luftaquila/monolith/device/TMA-1/Core/Src/sdio.c

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
/* Includes ------------------------------------------------------------------*/
#include "sdio.h"

/* USER CODE BEGIN 0 */
extern FIL logfile;
extern SYSTEM_STATE sys_state;
char logname[40];

LOG syslog_buffer;
extern ring_buffer_t SD_BUFFER;
extern uint8_t SD_BUFFER_ARR[1 << 12];

int SD_SETUP(DATETIME *boot) {
  FATFS SD_FATFS;

  // init buffer
  ring_buffer_init(&SD_BUFFER, (char *)SD_BUFFER_ARR, sizeof(SD_BUFFER_ARR));

  disk_initialize((BYTE) 0);
  int ret = f_mount(&SD_FATFS, "", 0);

  if (ret != FR_OK) {
    sys_state.SD = false;
    HAL_GPIO_WritePin(GPIOE, LED_SD_Pin, GPIO_PIN_RESET);

    DEBUG_MSG("[%8lu] [ERR] SD mount failed: %d\r\n", HAL_GetTick(), ret);
    SYS_LOG(LOG_ERROR, SYS, SYS_SD_FAIL);

    return ret;
  }

  sprintf(logname, "20%02d-%02d-%02d %02d-%02d-%02d.log",
      boot->year, boot->month, boot->date, boot->hour, boot->minute, boot->second);

  ret = f_open(&logfile, logname, FA_OPEN_APPEND | FA_WRITE);

  if (ret != FR_OK) {
    sys_state.SD = false;
    HAL_GPIO_WritePin(GPIOE, LED_SD_Pin, GPIO_PIN_RESET);

    DEBUG_MSG("[%8lu] [ERR] SD open failed: %d\r\n", HAL_GetTick(), ret);
    SYS_LOG(LOG_ERROR, SYS, SYS_SD_FAIL);

    return ret;
  }

  sys_state.SD = true;
  HAL_GPIO_WritePin(GPIOE, LED_SD_Pin, GPIO_PIN_SET);

  return SYS_OK;
}

int SD_WRITE(void) {
  if (sys_state.SD == false) {
    return -1;
  }

  if (ring_buffer_is_empty(&SD_BUFFER)) {
    return -1;
  }

  int ret = 0;
  static int32_t written_count;

  while (!ring_buffer_is_empty(&SD_BUFFER)) {
    ring_buffer_dequeue_arr(&SD_BUFFER, (char *)&syslog_buffer, sizeof(LOG));
    ret = f_write(&logfile, &syslog_buffer, sizeof(LOG), (void *)&written_count);
  }

  if (ret != FR_OK) {
    sys_state.SD = false;
    HAL_GPIO_WritePin(GPIOE, LED_SD_Pin, GPIO_PIN_RESET);

    DEBUG_MSG("[%8lu] [ERR] SD write failed: %d\r\n", HAL_GetTick(), ret);
    SYS_LOG(LOG_ERROR, SYS, SYS_SD_FAIL);
  }

  return ret;
}

int SD_SYNC(void) {
  if (sys_state.SD == false) {
    return -1;
  }

  int ret = f_sync(&logfile);

  if (ret != FR_OK) {
    sys_state.SD = false;
    HAL_GPIO_WritePin(GPIOE, LED_SD_Pin, GPIO_PIN_RESET);

    DEBUG_MSG("[%8lu] [ERR] SD sync failed: %d\r\n", HAL_GetTick(), ret);
    SYS_LOG(LOG_ERROR, SYS, SYS_SD_FAIL);
  }

  return ret;
}
/* USER CODE END 0 */

SD_HandleTypeDef hsd;
DMA_HandleTypeDef hdma_sdio_rx;
DMA_HandleTypeDef hdma_sdio_tx;

/* SDIO init function */

void MX_SDIO_SD_Init(void)
{

  hsd.Instance = SDIO;
  hsd.Init.ClockEdge = SDIO_CLOCK_EDGE_RISING;
  hsd.Init.ClockBypass = SDIO_CLOCK_BYPASS_DISABLE;
  hsd.Init.ClockPowerSave = SDIO_CLOCK_POWER_SAVE_DISABLE;
  hsd.Init.BusWide = SDIO_BUS_WIDE_1B;
  hsd.Init.HardwareFlowControl = SDIO_HARDWARE_FLOW_CONTROL_ENABLE;
  hsd.Init.ClockDiv = 12;
}

void HAL_SD_MspInit(SD_HandleTypeDef* sdHandle)
{

  GPIO_InitTypeDef GPIO_InitStruct = {0};
  if(sdHandle->Instance==SDIO)
  {
    /* SDIO clock enable */
    __HAL_RCC_SDIO_CLK_ENABLE();

    __HAL_RCC_GPIOC_CLK_ENABLE();
    __HAL_RCC_GPIOD_CLK_ENABLE();
    /**SDIO GPIO Configuration
    PC8     ------> SDIO_D0
    PC12     ------> SDIO_CK
    PD2     ------> SDIO_CMD
    */
    GPIO_InitStruct.Pin = GPIO_PIN_8;
    GPIO_InitStruct.Mode = GPIO_MODE_AF_PP;
    GPIO_InitStruct.Pull = GPIO_PULLUP;
    GPIO_InitStruct.Speed = GPIO_SPEED_FREQ_VERY_HIGH;
    GPIO_InitStruct.Alternate = GPIO_AF12_SDIO;
    HAL_GPIO_Init(GPIOC, &GPIO_InitStruct);

    GPIO_InitStruct.Pin = GPIO_PIN_12;
    GPIO_InitStruct.Mode = GPIO_MODE_AF_PP;
    GPIO_InitStruct.Pull = GPIO_NOPULL;
    GPIO_InitStruct.Speed = GPIO_SPEED_FREQ_VERY_HIGH;
    GPIO_InitStruct.Alternate = GPIO_AF12_SDIO;
    HAL_GPIO_Init(GPIOC, &GPIO_InitStruct);

    GPIO_InitStruct.Pin = GPIO_PIN_2;
    GPIO_InitStruct.Mode = GPIO_MODE_AF_PP;
    GPIO_InitStruct.Pull = GPIO_PULLUP;
    GPIO_InitStruct.Speed = GPIO_SPEED_FREQ_VERY_HIGH;
    GPIO_InitStruct.Alternate = GPIO_AF12_SDIO;
    HAL_GPIO_Init(GPIOD, &GPIO_InitStruct);

    /* SDIO DMA Init */
    /* SDIO_RX Init */
    hdma_sdio_rx.Instance = DMA2_Stream6;
    hdma_sdio_rx.Init.Channel = DMA_CHANNEL_4;
    hdma_sdio_rx.Init.Direction = DMA_PERIPH_TO_MEMORY;
    hdma_sdio_rx.Init.PeriphInc = DMA_PINC_DISABLE;
    hdma_sdio_rx.Init.MemInc = DMA_MINC_ENABLE;
    hdma_sdio_rx.Init.PeriphDataAlignment = DMA_PDATAALIGN_WORD;
    hdma_sdio_rx.Init.MemDataAlignment = DMA_MDATAALIGN_WORD;
    hdma_sdio_rx.Init.Mode = DMA_PFCTRL;
    hdma_sdio_rx.Init.Priority = DMA_PRIORITY_LOW;
    hdma_sdio_rx.Init.FIFOMode = DMA_FIFOMODE_ENABLE;
    hdma_sdio_rx.Init.FIFOThreshold = DMA_FIFO_THRESHOLD_FULL;
    hdma_sdio_rx.Init.MemBurst = DMA_MBURST_INC4;
    hdma_sdio_rx.Init.PeriphBurst = DMA_PBURST_INC4;
    if (HAL_DMA_Init(&hdma_sdio_rx) != HAL_OK)
    {
      Error_Handler();
    }

    __HAL_LINKDMA(sdHandle,hdmarx,hdma_sdio_rx);

    /* SDIO_TX Init */
    hdma_sdio_tx.Instance = DMA2_Stream3;
    hdma_sdio_tx.Init.Channel = DMA_CHANNEL_4;
    hdma_sdio_tx.Init.Direction = DMA_MEMORY_TO_PERIPH;
    hdma_sdio_tx.Init.PeriphInc = DMA_PINC_DISABLE;
    hdma_sdio_tx.Init.MemInc = DMA_MINC_ENABLE;
    hdma_sdio_tx.Init.PeriphDataAlignment = DMA_PDATAALIGN_WORD;
    hdma_sdio_tx.Init.MemDataAlignment = DMA_MDATAALIGN_WORD;
    hdma_sdio_tx.Init.Mode = DMA_PFCTRL;
    hdma_sdio_tx.Init.Priority = DMA_PRIORITY_LOW;
    hdma_sdio_tx.Init.FIFOMode = DMA_FIFOMODE_ENABLE;
    hdma_sdio_tx.Init.FIFOThreshold = DMA_FIFO_THRESHOLD_FULL;
    hdma_sdio_tx.Init.MemBurst = DMA_MBURST_INC4;
    hdma_sdio_tx.Init.PeriphBurst = DMA_PBURST_INC4;
    if (HAL_DMA_Init(&hdma_sdio_tx) != HAL_OK)
    {
      Error_Handler();
    }

    __HAL_LINKDMA(sdHandle,hdmatx,hdma_sdio_tx);

    /* SDIO interrupt Init */
    HAL_NVIC_SetPriority(SDIO_IRQn, 0, 0);
    HAL_NVIC_EnableIRQ(SDIO_IRQn);
  }
}

void HAL_SD_MspDeInit(SD_HandleTypeDef* sdHandle)
{

  if(sdHandle->Instance==SDIO)
  {
    /* Peripheral clock disable */
    __HAL_RCC_SDIO_CLK_DISABLE();

    /**SDIO GPIO Configuration
    PC8     ------> SDIO_D0
    PC12     ------> SDIO_CK
    PD2     ------> SDIO_CMD
    */
    HAL_GPIO_DeInit(GPIOC, GPIO_PIN_8|GPIO_PIN_12);

    HAL_GPIO_DeInit(GPIOD, GPIO_PIN_2);

    /* SDIO DMA DeInit */
    HAL_DMA_DeInit(sdHandle->hdmarx);
    HAL_DMA_DeInit(sdHandle->hdmatx);

    /* SDIO interrupt Deinit */
    HAL_NVIC_DisableIRQ(SDIO_IRQn);
  }
}
