luftaquila/monolith/device/TMA-1/Core/Inc/logger.h

/*
 * logger.h
 *
 *  Created on: Sep 10, 2023
 *      Author: LUFT-AQUILA
 */

#ifndef CORE_INC_LOGGER_H_
#define CORE_INC_LOGGER_H_

/* system log structure */
typedef struct {
  uint32_t timestamp;
  uint8_t level;
  uint8_t source;
  uint8_t key;
  uint8_t checksum;
  uint8_t value[8];
} LOG;

/* log level type */
typedef enum {
  LOG_FATAL = 0,
  LOG_ERROR,
  LOG_WARN,
  LOG_INFO,
  LOG_DEBUG,
} LOG_LEVEL;

/* log source types */
typedef enum {
  SYS = 0,
  CAN,
  DIGITAL,
  ANALOG,
  PULSE,
  ACCELEROMETER,
  GPS,
} LOG_SOURCE;

/* log key types per sources */
typedef enum {
  SYS_SD_INIT = 0,
  SYS_CORE_INIT,
  SYS_SERIAL_INIT,
  SYS_TELEMETRY_REMOTE,
  SYS_TELEMETRY_INIT,
  CAN_INIT,
  DIGITAL_INIT,
  ANALOG_INIT,
  PULSE_INIT,
  ACCELEROMETER_INIT,
  GPS_INIT,
  SYS_READY,
  SYS_RTC_FIX,
  SYS_SD_FAIL,
  CAN_ERR_CANERR,
  CAN_ERR_RXMSGFAIL,
  CAN_ERR_FIFOFULL
} LOG_KEY_SYS;

typedef enum {
  DIGITAL_DATA = 0,
} LOG_KEY_DIGITAL;

typedef enum {
  ANALOG_SYS = 0,
  ANALOG_DATA
} LOG_KEY_ANALOG;

typedef enum {
  PULSE_DATA = 0,
} LOG_KEY_PULSE;

typedef enum {
  ACCELEROMETER_DATA = 0,
} LOG_KEY_ACCELEROMETER;

typedef enum {
  GPS_POS = 0,
  GPS_VEC,
  GPS_TIME
} LOG_KEY_GPS;

/* Prototypes */
int SYS_LOG(LOG_LEVEL level, LOG_SOURCE source, int key);

/* macro for debug print */
#ifdef DEBUG_MODE
#define DEBUG_MSG(f_, ...) printf((f_), ##__VA_ARGS__)
#else
#define DEBUG_MSG(f_, ...)
#endif

#endif /* CORE_INC_LOGGER_H_ */
